NA-varez/Nixie_Tester_IN-1_IN-12A/media/1.jpg

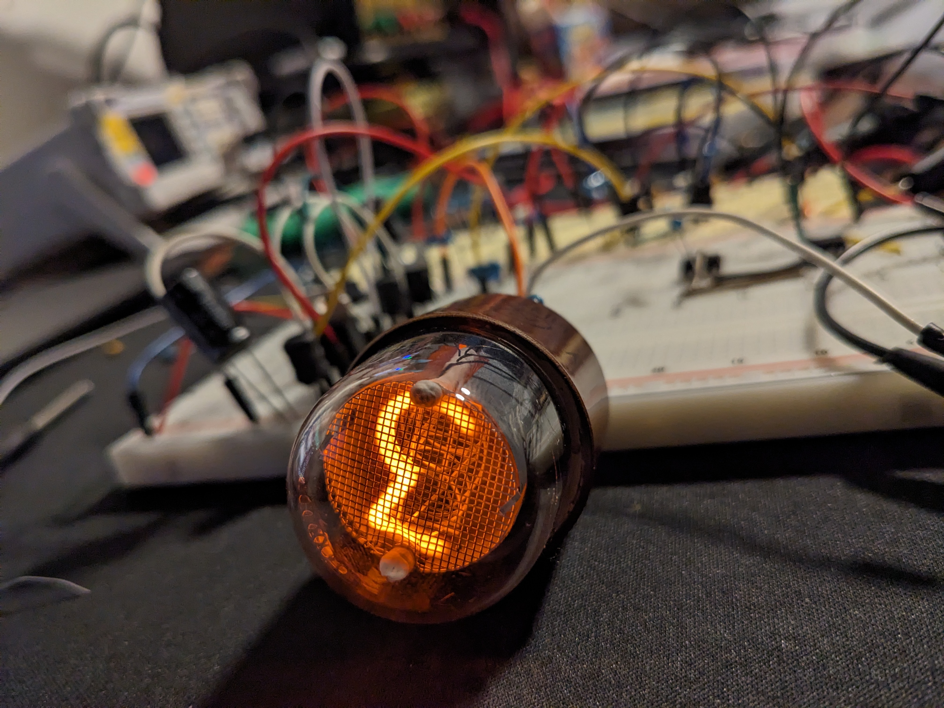
media/1.jpg
