NA-varez/Nixie_Tester_IN-1_IN-12A/media/PXL_20231227_110331705.jpg

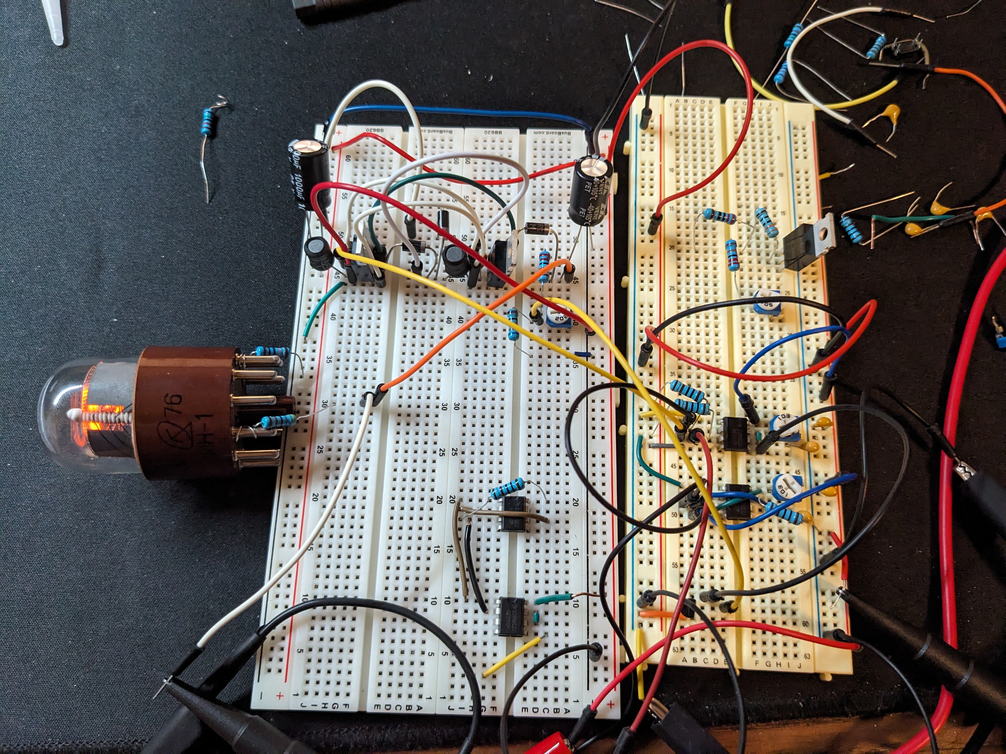
media/PXL_20231227_110331705.jpg
